vrees/Esp32LoraBoard/src/sleep-wakeup.h

#ifndef _SLEEP_WAKEUP_H_
#define _SLEEP_WAKEUP_H_

#ifdef __cplusplus
extern "C"
{
#endif

    typedef enum
    {
        TIMER_WAKEUP = 1,     // Wakeup by timer
        LOW_LEVEL_WAKEUP = 2, // Water level sensor detected low level and initiated wakeup
        DEBUG_WAKEUP = 3,     // User pressed reset button
    } operation_mode_t;

    extern operation_mode_t operation_mode;

    void wakeupAndInit();
    void powerOffAndSleep();

#ifdef __cplusplus
}
#endif

#endif
