vrees/Esp32LoraBoard/src/power.h

#ifndef _POWER_H_
#define _POWER_H_

#ifdef __cplusplus
extern "C"
{
#endif

    void initIoPorts();

    void enablePeripheralPower();
    void disablePeripheralPower();

    void enableBatteryVoltageMeasurement();
    void disableBatteryVoltageMeasurement();

    void enableExternalVoltageMeasurement();
    void disableExternalVoltageMeasurement();

#ifdef __cplusplus
}
#endif
#endif
